andredemari/diyBMSv4/ATTINYCellModule/src/packet_processor.cpp

/*
____  ____  _  _  ____  __  __  ___
(  _ \(_  _)( \/ )(  _ \(  \/  )/ __)
)(_) )_)(_  \  /  ) _ < )    ( \__ \
(____/(____) (__) (____/(_/\/\_)(___/

DIYBMS V4.0
CELL MODULE FOR ATTINY841

(c)2019 Stuart Pittaway

COMPILE THIS CODE USING PLATFORM.IO

LICENSE
Attribution-NonCommercial-ShareAlike 2.0 UK: England & Wales (CC BY-NC-SA 2.0 UK)
https://creativecommons.org/licenses/by-nc-sa/2.0/uk/

* Non-Commercial — You may not use the material for commercial purposes.
* Attribution — You must give appropriate credit, provide a link to the license, and indicate if changes were made.
  You may do so in any reasonable manner, but not in any way that suggests the licensor endorses you or your use.
* ShareAlike — If you remix, transform, or build upon the material, you must distribute your
  contributions under the same license as the original.
* No additional restrictions — You may not apply legal terms or technological measures
  that legally restrict others from doing anything the license permits.
*/

#include "packet_processor.h"
//Function to populate settings from packet DJ
void PacketProcessor::PacketToConfig() {
  FLOATUNION_t myFloat;

  myFloat.word[0] = buffer.moduledata[0];
  myFloat.word[1] = buffer.moduledata[1];
  if (myFloat.number < 0xFFFF) {
    _config->LoadResistance = myFloat.number;
  }

  myFloat.word[0] = buffer.moduledata[2];
  myFloat.word[1] = buffer.moduledata[3];

  if (myFloat.number < 0xFFFF) {
    _config->Calibration = myFloat.number;
  }

  myFloat.word[0] = buffer.moduledata[4];
  myFloat.word[1] = buffer.moduledata[5];
  if (myFloat.number < 0xFFFF) {
    _config->mVPerADC = myFloat.number;
  }

  if (buffer.moduledata[6] != 0xFF) {
    _config->BypassOverTempShutdown = buffer.moduledata[6];
  }

  if (buffer.moduledata[7] != 0xFFFF) {
    _config->BypassThresholdmV = buffer.moduledata[7];
  }
  if (buffer.moduledata[8] != 0xFFFF) {
    _config->Internal_BCoefficient = buffer.moduledata[8];
  }

  if (buffer.moduledata[9] != 0xFFFF) {
    _config->External_BCoefficient = buffer.moduledata[9];
  }
}


// Increases the incoming packets address before sending to the next module
void PacketProcessor::incrementPacketAddress() {
  //See Issue #11 prevent address 16 rolling over and increasing bank address
  buffer.address = (buffer.address & 0xF0) + (((buffer.address & 0x0F) + 1) & 0x0F);
}

//Returns TRUE if the internal thermistor is hotter than the required setting
bool PacketProcessor::BypassOverheatCheck() {
  return (InternalTemperature() > _config->BypassOverTempShutdown);
}

// Returns an integer byte indicating the internal thermistor temperature in degrees C
// uses basic B Coefficient Steinhart calculaton to give rough approximation in temperature
int16_t PacketProcessor::InternalTemperature() {
  return Steinhart::ThermistorToCelcius(_config->Internal_BCoefficient, onboard_temperature, Ro_ONBOARD);
}

//Returns TRUE if the cell voltage is greater than the required setting
bool PacketProcessor::BypassCheck() {
  return (CellVoltage() > _config->BypassThresholdmV);
}

//Determines if a received packet of instruction is for this module
//based on broadcast flag, bank id and module address
bool PacketProcessor::isPacketForMe() {
  //Modules can be grouped together in banks - only allow processing of packets in the correct bank
  if (((buffer.address & 0x30) >> 4) != _config->mybank) return false;

  //Broadcast for my bank?
  if ((buffer.address & 0x80) == 0x80) {
    //If we receive a broadcast message whatever address is received is my unique module address
    //so store it for later use
    mymoduleaddress = buffer.address & 0x0F;

    //Ensure the next module has a higher address
    incrementPacketAddress();
    return true;
  }

  //Is this packet addressed directly to me?
  if ((buffer.address & 0x0F) == mymoduleaddress && mymoduleaddress != 0xFF) return true;

  return false;
}

//Records an ADC reading after the interrupt has finished
void PacketProcessor::ADCReading(uint16_t value) {
  switch (adcmode) {
  case ADC_CELL_VOLTAGE:
    {
      //UpdateRingBuffer(value);
      raw_adc_voltage = value;
      break;
    }
  case ADC_INTERNAL_TEMP:
    {
      onboard_temperature = value;
      break;
    }
  case ADC_EXTERNAL_TEMP:
    {
      external_temperature = value;
      break;
    }
  }
}

//Start an ADC reading via Interrupt
void PacketProcessor::TakeAnAnalogueReading(uint8_t mode) {
  adcmode = mode;

  switch (adcmode) {
  case ADC_CELL_VOLTAGE:
    {
      _hardware-> SelectCellVoltageChannel();
      break;
    }
  case ADC_INTERNAL_TEMP:
    {
      _hardware-> SelectInternalTemperatureChannel();
      break;
    }
  case ADC_EXTERNAL_TEMP:
    {
      _hardware-> SelectExternalTemperatureChannel();
      break;
    }
  default:
    //Avoid taking a reading if we get to here
    return;
  }

  _hardware-> BeginADCReading();
}

//Returns the memory address of the internal buffer
byte* PacketProcessor::GetBufferPointer() {
  return (byte*)&buffer;
}

//Returns the byte size of the internal buffer
int PacketProcessor::GetBufferSize() {
  return sizeof(buffer);
}

//Run when a new packet is received over serial
bool PacketProcessor::onPacketReceived(const uint8_t* receivebuffer, size_t len) {
  // Process your decoded incoming packet here.
  //Copy to our buffer (probably a better way to share memory than this)
  memcpy(&buffer, receivebuffer, sizeof(buffer));   //Moved by DJ to avoid repeating old packets
  if (len == sizeof(buffer)) {

    //Copy to our buffer (probably a better way to share memory than this)
    //memcpy(&buffer, receivebuffer, sizeof(buffer));

    //Calculate the CRC and compare to received
    uint16_t validateCRC = CRC16::CalculateArray((unsigned char*)&buffer, sizeof(buffer) - 2);

    if (validateCRC == buffer.crc) {
      //It's a good packet
      if (isPacketForMe()) {
        if (processPacket()) {

          //Set flag to indicate we processed packet
          buffer.command = buffer.command | B10000000;

          //Calculate new checksum over whole buffer
          buffer.crc = CRC16::CalculateArray((unsigned char*)&buffer, sizeof(buffer) - 2);

          //Return true if we processed the packet
          return true;
        }
      }

      //Return false the packet was not for me (but still a valid packet)...
      return false;
    }
  }

  //We need to do something here, the packet received was not correct
  badpackets++;
  return false;
}

//Read cell voltage and return millivolt reading (16 bit unsigned)
uint16_t PacketProcessor::CellVoltage() {
  //TODO: Get rid of the need for float variables?
  float v = ((float) raw_adc_voltage * _config->mVPerADC) * _config->Calibration;

  return (uint16_t) v;
}

//Returns the last RAW ADC value 0-1023
uint16_t PacketProcessor::RawADCValue() {
  return raw_adc_voltage;
}

// Process the request in the received packet
//command byte
// RRRR CCCC
// X    = 1 bit indicate if packet processed
// R    = 3 bits reserved not used
// C    = 4 bits command (16 possible commands)
bool PacketProcessor::processPacket() {
  switch (buffer.command & 0x0F) {

  case COMMAND::SetBankIdentity:
    {
      //Set this modules bank address and store in EEPROM
      _config->mybank = buffer.moduledata[mymoduleaddress] & 0x3;

      //Save settings
      Settings::WriteConfigToEEPROM((uint8_t*)_config, sizeof(CellModuleConfig), EEPROM_CONFIG_ADDRESS);

      //Indicate we processed this packet
      buffer.moduledata[mymoduleaddress] = 0xFFFF;
      return true;
    }

  case COMMAND::ReadVoltageAndStatus:
    {
      //Read voltage of VCC
      //Maximum voltage 8191mV
      buffer.moduledata[mymoduleaddress] = CellVoltage() & 0x1FFF;

      //3 top bits
      //X = In bypass
      //Y = Bypass over temperature
      //Z = Not used

      if (BypassOverheatCheck()) {
        buffer.moduledata[mymoduleaddress] = buffer.moduledata[mymoduleaddress] | 0x4000;
      }

      if (WeAreInBypass) {
        buffer.moduledata[mymoduleaddress] = buffer.moduledata[mymoduleaddress] | 0x8000;
      }

      return true;
    }

  case COMMAND::Identify:
    {
      //identify module
      //Indicate that we received and did something
      buffer.moduledata[mymoduleaddress] = 0xFFFF;

      //For the next 10 received packets - keep the LEDs lit up
      identifyModule = 10;
      return true;
    }

  case COMMAND::ReadTemperature:
    {
      //Read the last 2 temperature values recorded by the ADC (both internal and external)
      buffer.moduledata[mymoduleaddress] = TemperatureMeasurement();
      return true;
    }

  case COMMAND::ReadBadPacketCounter:
    {
      //Report number of bad packets
      buffer.moduledata[mymoduleaddress] = badpackets;
      return true;
    }

  case COMMAND::ReadSettings:
    {
      //Report settings/configuration

      FLOATUNION_t myFloat;
      myFloat.number = _config->LoadResistance;
      buffer.moduledata[0] = myFloat.word[0];
      buffer.moduledata[1] = myFloat.word[1];

      myFloat.number = _config->Calibration;
      buffer.moduledata[2] = myFloat.word[0];
      buffer.moduledata[3] = myFloat.word[1];

      myFloat.number = _config->mVPerADC;
      buffer.moduledata[4] = myFloat.word[0];
      buffer.moduledata[5] = myFloat.word[1];

      buffer.moduledata[6] = _config->BypassOverTempShutdown;
      buffer.moduledata[7] = _config->BypassThresholdmV;
      buffer.moduledata[8] = _config->Internal_BCoefficient;
      buffer.moduledata[9] = _config->External_BCoefficient;

      return true;
    }

  case COMMAND::WriteSettings:
    {
      PacketToConfig();       //Populate Config from Packet  DJ
      Settings::WriteConfigToEEPROM((uint8_t*)_config, sizeof(CellModuleConfig), EEPROM_CONFIG_ADDRESS);

      return true;
    }

  case COMMAND::VolatileSettings:
    {
      PacketToConfig();       //Populate Config from Packet  DJ
      return true;
    }

  }

  return false;
}

uint16_t PacketProcessor::TemperatureMeasurement() {
  return (Steinhart::TemperatureToByte(Steinhart::ThermistorToCelcius(_config->Internal_BCoefficient, onboard_temperature, Ro_ONBOARD)) << 8) +
    Steinhart::TemperatureToByte(Steinhart::ThermistorToCelcius(_config->External_BCoefficient, external_temperature, Ro_EXTERNAL));
}
