andredemari/diyBMSv4/ESPController/include/logo.h

// GIF LOGO
// Converted to hex by
// http://tomeko.net/online_tools/file_to_hex.php?lang=en

#define FILE_LOGO_SIZE_BYTES 4352

const uint8_t FILE_LOGO  [] PROGMEM =
{
  0x47, 0x49, 0x46, 0x38, 0x37, 0x61, 0xBF, 0x00, 0x30, 0x00, 0xE7, 0xFD, 0x00, 0x00, 0x01, 0x00,
  0x06, 0x00, 0x00, 0x00, 0x02, 0x00, 0x00, 0x03, 0x06, 0x01, 0x04, 0x00, 0x03, 0x05, 0x01, 0x00,
  0x06, 0x09, 0x06, 0x09, 0x04, 0x03, 0x0A, 0x0D, 0x05, 0x0B, 0x0E, 0x08, 0x0B, 0x07, 0x06, 0x0D,
  0x10, 0x0B, 0x0D, 0x0A, 0x0B, 0x11, 0x13, 0x10, 0x11, 0x0E, 0x11, 0x13, 0x10, 0x0F, 0x14, 0x16,
  0x11, 0x15, 0x17, 0x13, 0x17, 0x19, 0x15, 0x19, 0x1B, 0x16, 0x1A, 0x1C, 0x5B, 0x00, 0x53, 0x5A,
  0x01, 0x59, 0x18, 0x1B, 0x1D, 0x60, 0x00, 0x5A, 0x61, 0x00, 0x5B, 0x62, 0x00, 0x5C, 0x63, 0x00,
  0x5D, 0x64, 0x00, 0x5E, 0x5C, 0x03, 0x5A, 0x61, 0x01, 0x63, 0x65, 0x01, 0x5F, 0x1A, 0x1E, 0x20,
  0x63, 0x03, 0x64, 0x66, 0x03, 0x60, 0x64, 0x05, 0x65, 0x1D, 0x21, 0x23, 0x65, 0x06, 0x66, 0x1F,
  0x23, 0x25, 0x66, 0x08, 0x67, 0x21, 0x25, 0x27, 0x67, 0x0A, 0x68, 0x22, 0x26, 0x28, 0x68, 0x0C,
  0x69, 0x24, 0x28, 0x2A, 0x69, 0x0E, 0x6A, 0x6B, 0x10, 0x6C, 0x27, 0x2B, 0x2D, 0x28, 0x2C, 0x2E,
  0x6C, 0x12, 0x6D, 0x29, 0x2D, 0x2F, 0x6D, 0x14, 0x6E, 0x2B, 0x2F, 0x31, 0x6F, 0x16, 0x70, 0x2D,
  0x31, 0x33, 0x2E, 0x32, 0x34, 0x6C, 0x1C, 0x70, 0x2F, 0x34, 0x36, 0x31, 0x35, 0x37, 0x6E, 0x1F,
  0x73, 0x33, 0x37, 0x39, 0x70, 0x21, 0x74, 0x36, 0x3A, 0x3C, 0x72, 0x23, 0x76, 0x37, 0x3B, 0x3D,
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
  0xD0, 0xDC, 0xC5, 0xCD, 0xE2, 0xBE, 0xD2, 0xDE, 0xC7, 0xCF, 0xE5, 0xC9, 0xD1, 0xE6, 0xC1, 0xD5,
  0xE2, 0xCB, 0xD3, 0xE8, 0xCD, 0xD4, 0xEA, 0xC4, 0xD8, 0xE4, 0xCE, 0xD6, 0xEB, 0xC8, 0xD8, 0xEC,
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
};
