andredemari/diyBMSv4/ESPController/include/SoftAP.h

#ifndef SOFTAP_H_
#define SOFTAP_H_




#include <Arduino.h>
#include <WiFi.h>
#include <Hash.h>
#include <AsyncTCP.h>
#include <ESPAsyncWebServer.h>
#include "settings.h"


struct wifi_eeprom_settings {
  char wifi_ssid[32 + 1];
  char wifi_passphrase[63 + 1];
};

class DIYBMSSoftAP {
   public:
      static void SetupAccessPoint(AsyncWebServer  *webserver);
      static bool LoadConfigFromEEPROM();
      static char* WifiSSID();
      static char* WifiPassword();

  private:
      static AsyncWebServer * _myserver;
      static void handleNotFound(AsyncWebServerRequest *request);

      static void handleRoot(AsyncWebServerRequest *request);
      static void handleSave(AsyncWebServerRequest *request);


      static String htmlHeader();
      static String htmlFooter();

      static wifi_eeprom_settings _config;
      static String networks;
};


#endif
